Taro-Hayashi/co2monitor/img/IMG_2476.jpeg

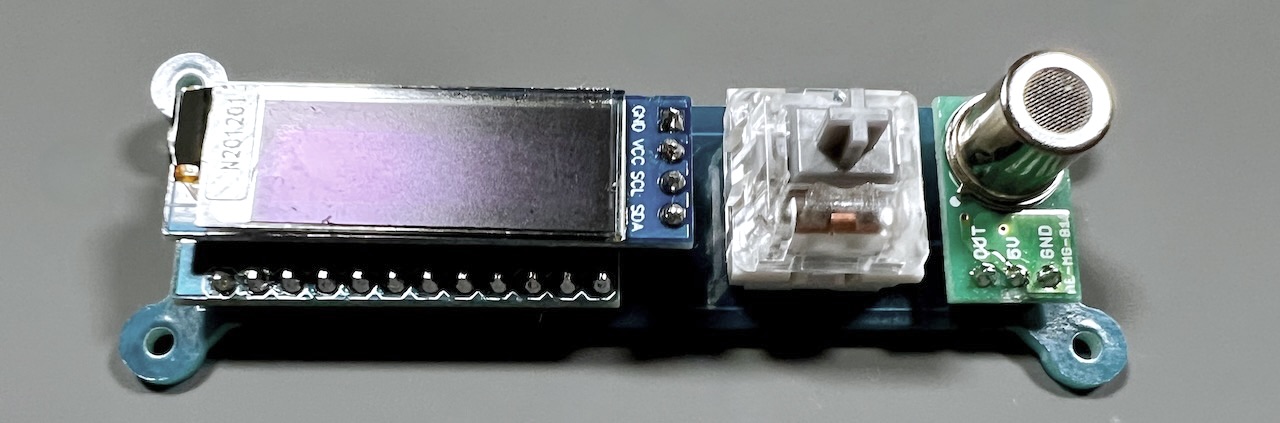
img/IMG_2476.jpeg
