Taro-Hayashi/co2monitor/img/IMG_2478.jpeg

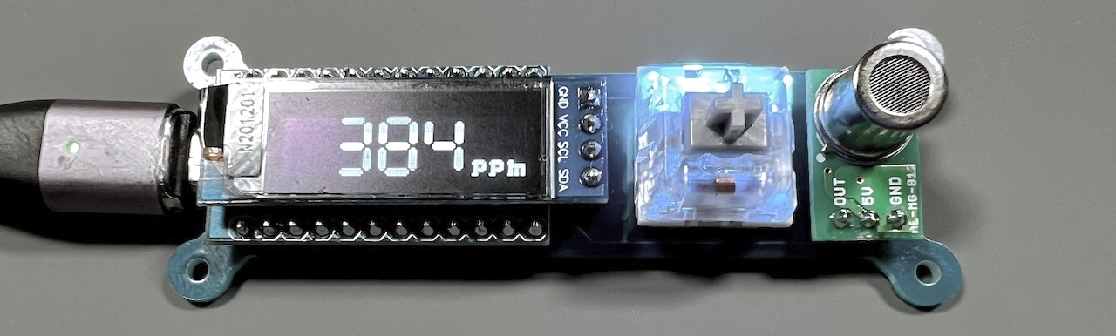
img/IMG_2478.jpeg
